mirage335/Mirage335BiosignalAmp/enclosures/Headset/SpongeAttachment.SLDPRT

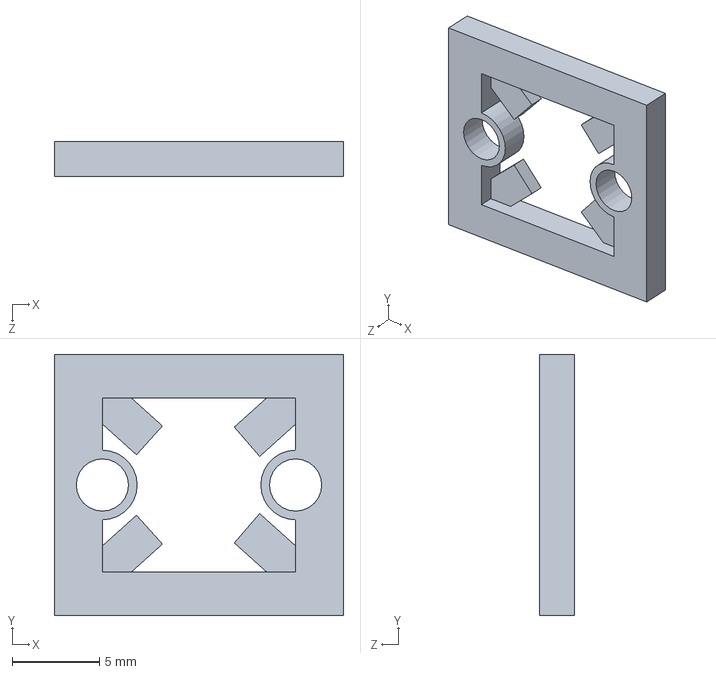
[picture p18: CAD file, 2014-01-24]
enclosures/Headset/SpongeAttachment.SLDPRT
16.6 x 15.0 x 2.00 mm
